ruxandradiaconu/Openbook-ebook-reader/Images/final_completed_back_view.png

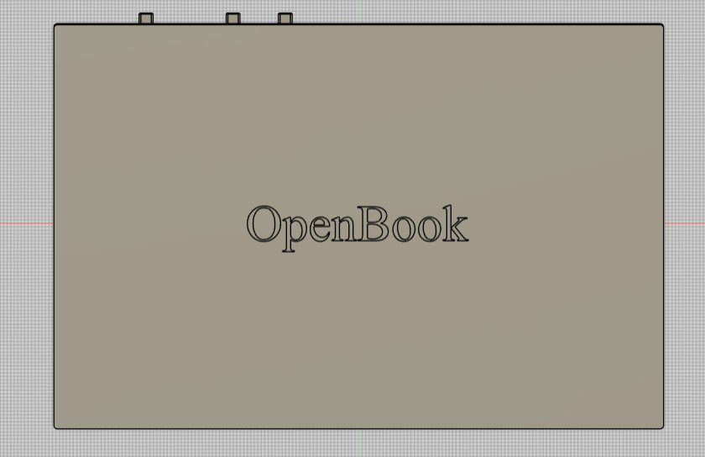
Images/final_completed_back_view.png
