ruxandradiaconu/Openbook-ebook-reader/Images/final_pcb_2d.png

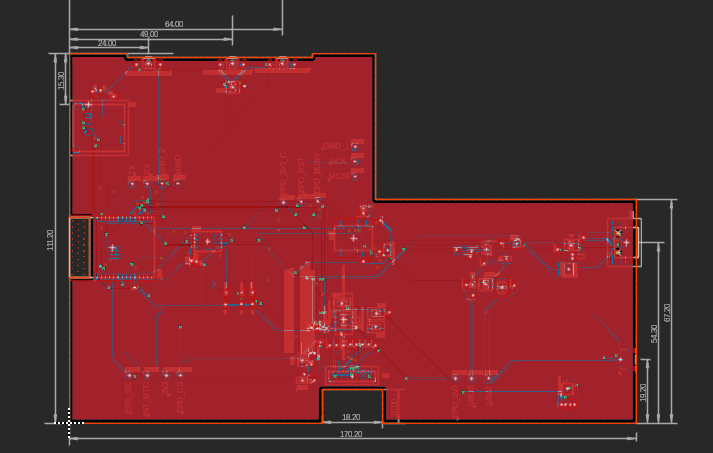
Images/final_pcb_2d.png
