ruxandradiaconu/Openbook-ebook-reader/Images/Screenshot 2025-04-06 130659.png

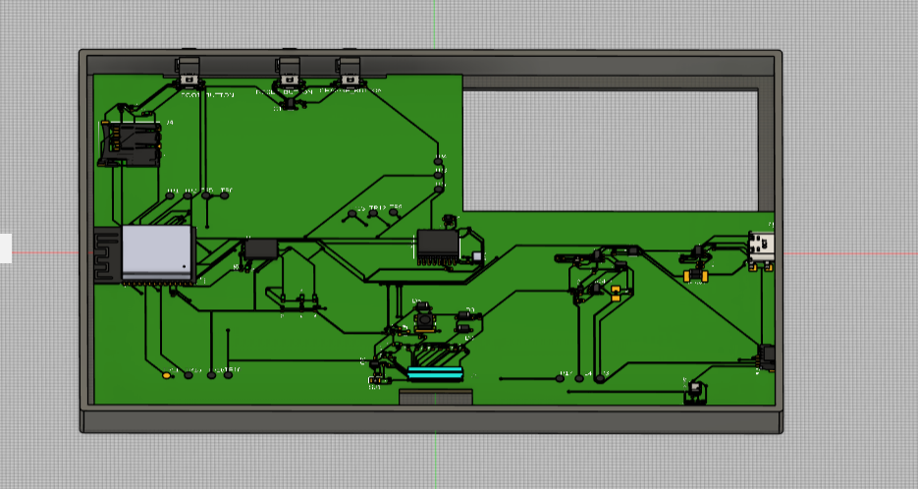
Images/Screenshot 2025-04-06 130659.png
