ruxandradiaconu/Openbook-ebook-reader/Images/Screenshot 2025-04-06 185355.png

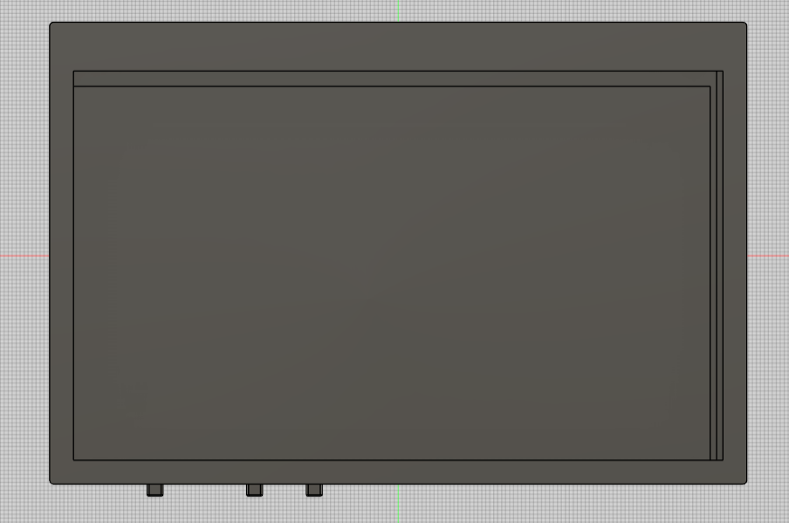
Images/Screenshot 2025-04-06 185355.png
